xunker/blue-gs/images/bluegs_v1.2_board_front_annotated.jpg

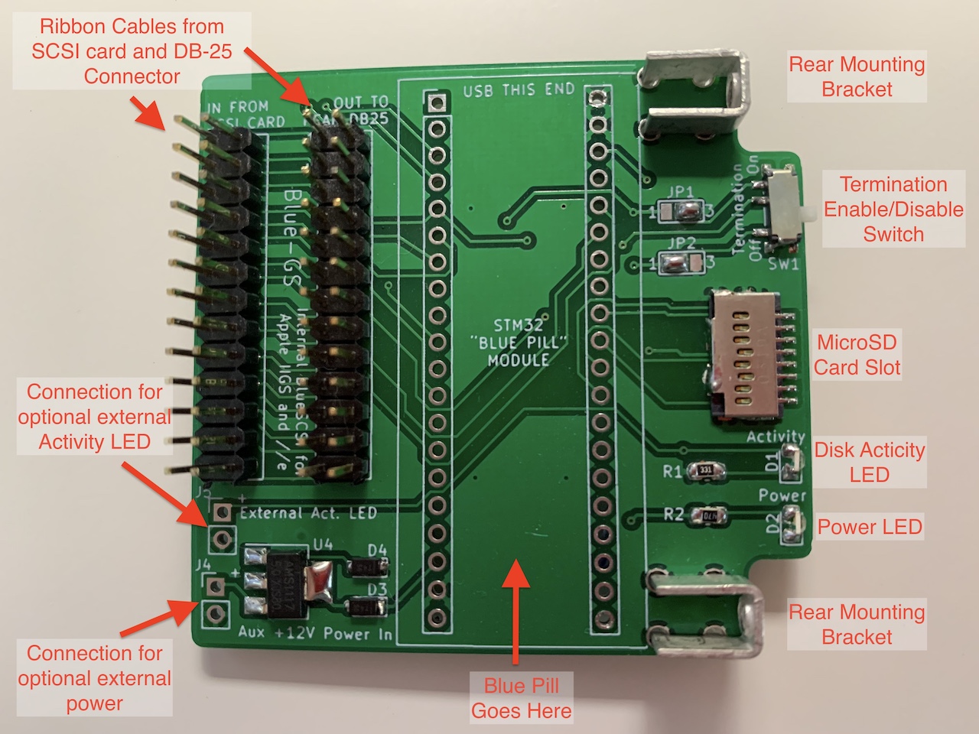
images/bluegs_v1.2_board_front_annotated.jpg
