xunker/blue-gs/images/bluegs_v1.2_board_rear_annotated.jpg

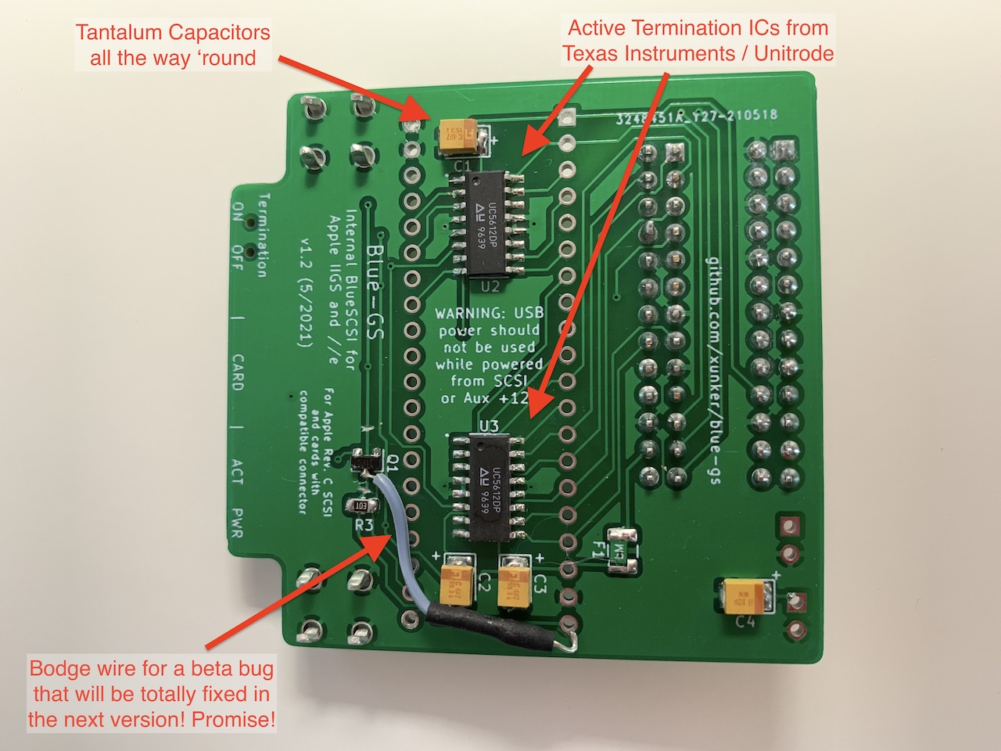
images/bluegs_v1.2_board_rear_annotated.jpg
