xunker/blue-gs/images/bluescsi_iigs_internal_v1.2_back.jpg

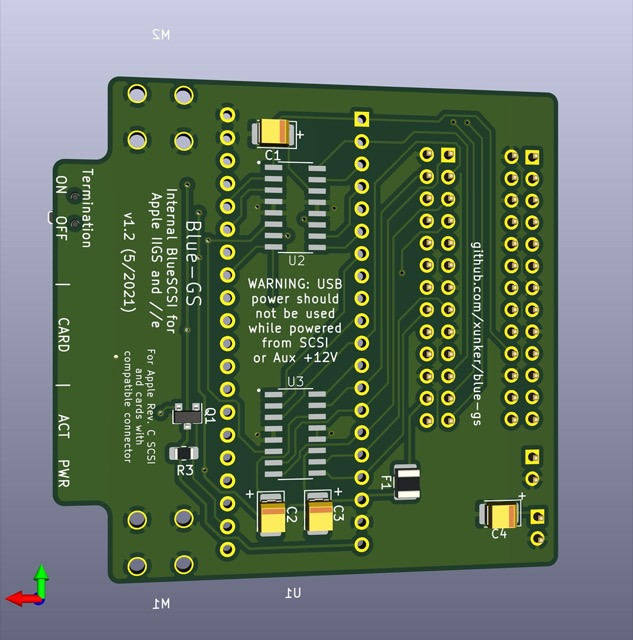
images/bluescsi_iigs_internal_v1.2_back.jpg
